LaboratoryStuff/Thorlabs/THR-100-010 Cage Slit 1mm/Photos/THR-100-010_Photo_02.JPG

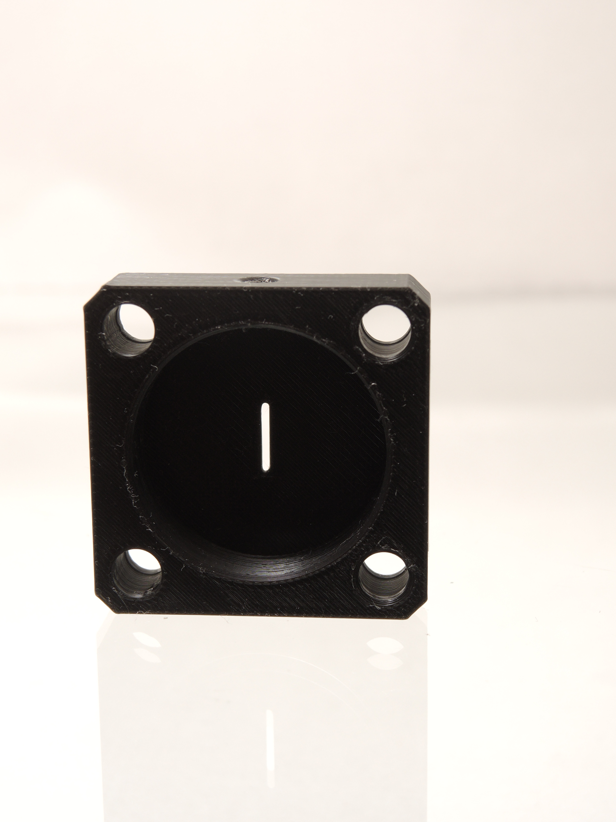
THR-100-010 Cage Slit 1mm/Photos/THR-100-010_Photo_02.JPG
