LaboratoryStuff/Thorlabs/THR-101-010 Cage Hamamatsu 14 x 14 mm/Drawing/THR-101-010-110_Drawing04.jpg

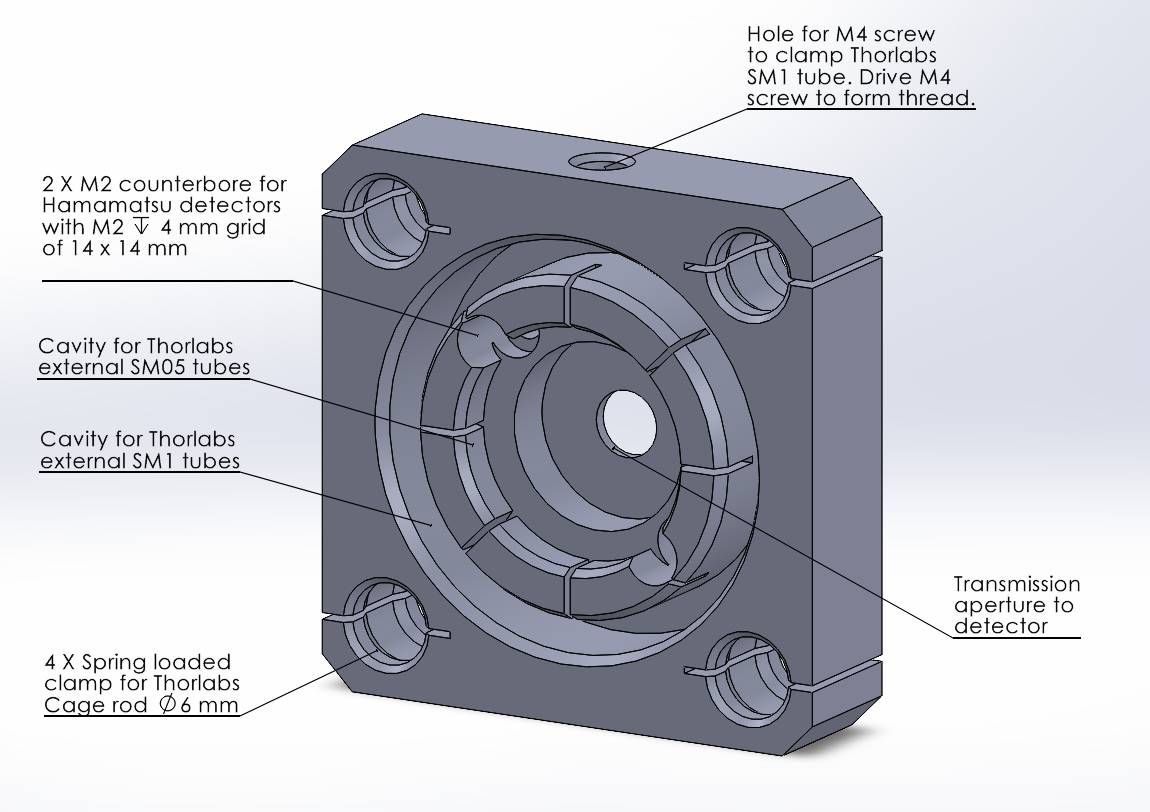
THR-101-010 Cage Hamamatsu 14 x 14 mm/Drawing/THR-101-010-110_Drawing04.jpg
