LaboratoryStuff/Thorlabs/THR-101-110 Cage Hamamatsu A3179/Photos/THR-101-110_Photo03.JPG

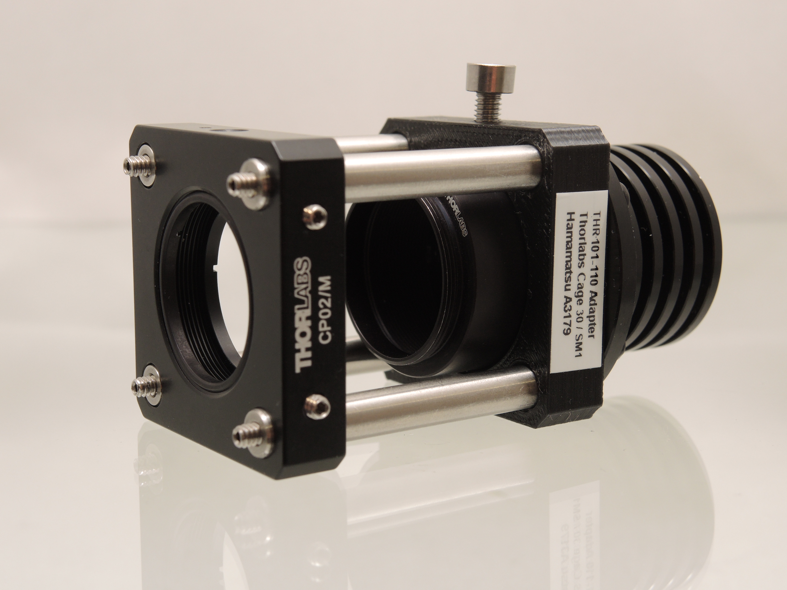
THR-101-110 Cage Hamamatsu A3179/Photos/THR-101-110_Photo03.JPG
