LaboratoryStuff/Thorlabs/THR-102-050 Aperture 5mm/Drawings/THR-102-050-110_Drawing04.jpg

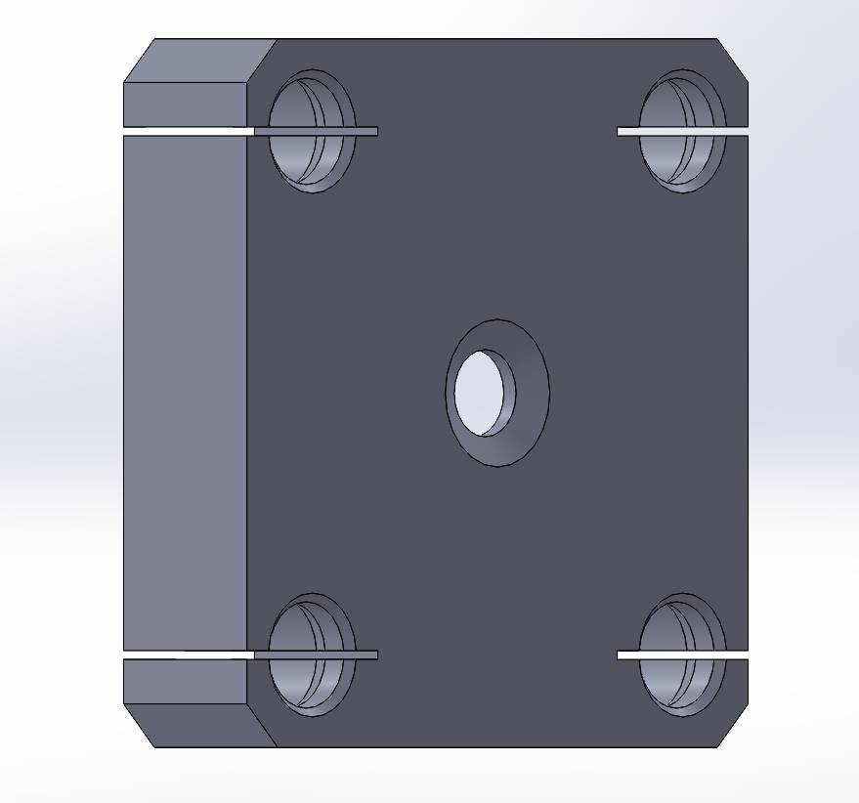
THR-102-050 Aperture 5mm/Drawings/THR-102-050-110_Drawing04.jpg
