LaboratoryStuff/Thorlabs/THR-102-050 Aperture 5mm/Photos/THR-102-050_Photo04.JPG

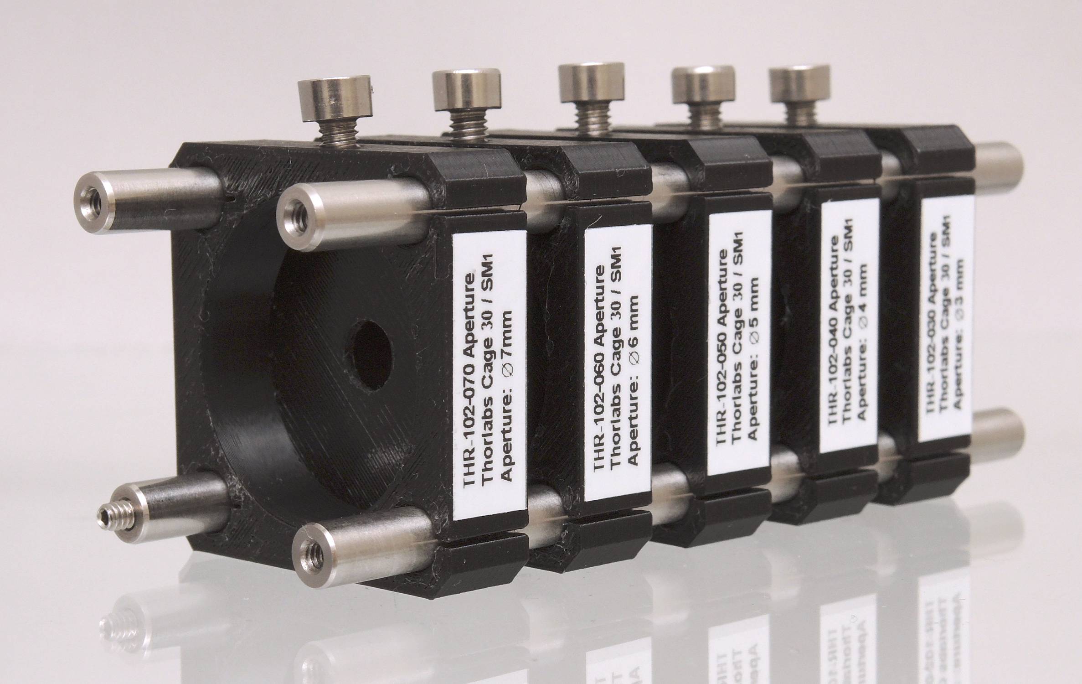
THR-102-050 Aperture 5mm/Photos/THR-102-050_Photo04.JPG
