LaboratoryStuff/Thorlabs/THR-120-010 Cage 60 SM2/Drawings/THR-120-010-010_Drawing03_cross-section.jpg

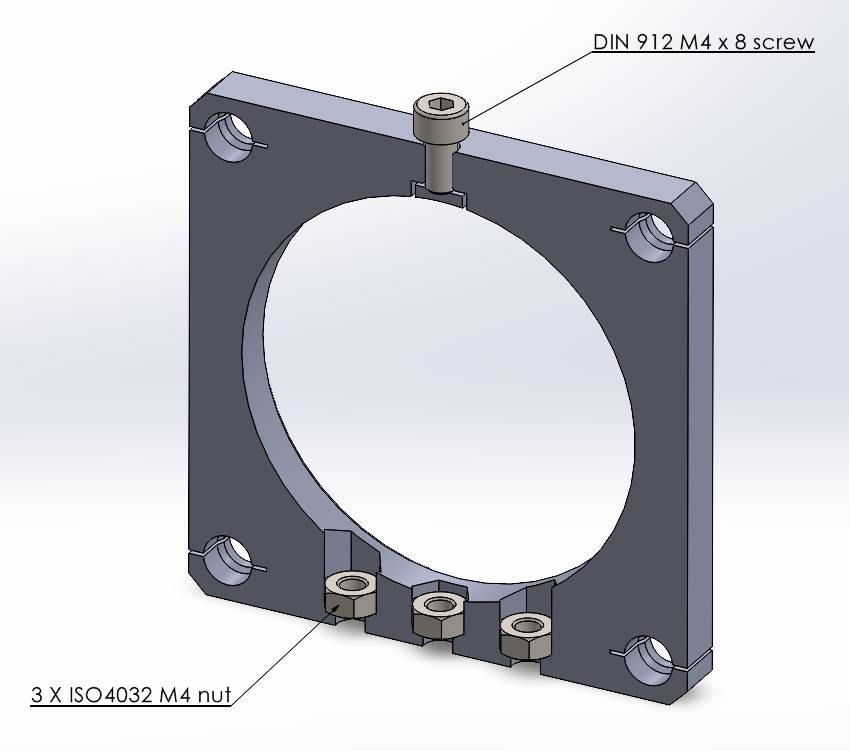
THR-120-010 Cage 60 SM2/Drawings/THR-120-010-010_Drawing03_cross-section.jpg
