LaboratoryStuff/Thorlabs/THR-120-010 Cage 60 SM2/Drawings/THR-120-010-110_Drawing02.jpg

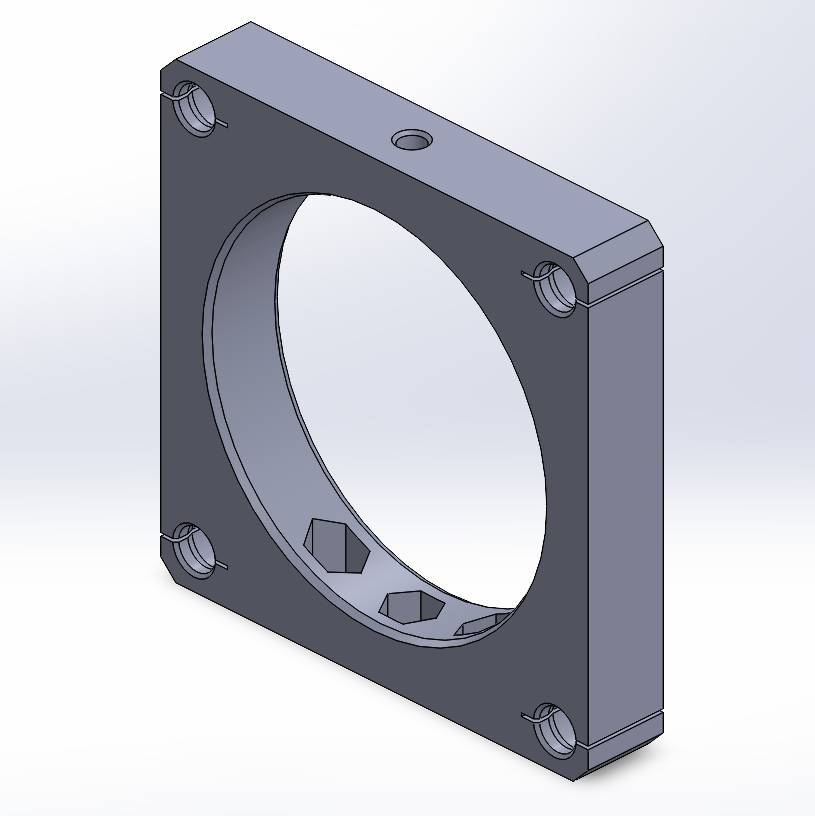
THR-120-010 Cage 60 SM2/Drawings/THR-120-010-110_Drawing02.jpg
