LaboratoryStuff/Thorlabs/THR-120-010 Cage 60 SM2/Drawings/THR-120-010-110_Drawing04_cross-section.jpg

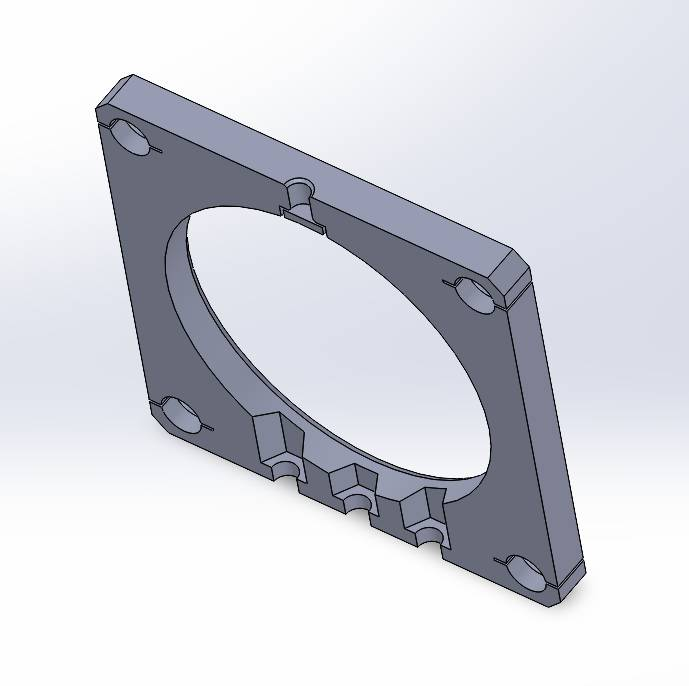
THR-120-010 Cage 60 SM2/Drawings/THR-120-010-110_Drawing04_cross-section.jpg
