LaboratoryStuff/Thorlabs/THR-120-010 Cage 60 SM2/Photos/THR-120-010_Photo_02_Add_Nut.JPG

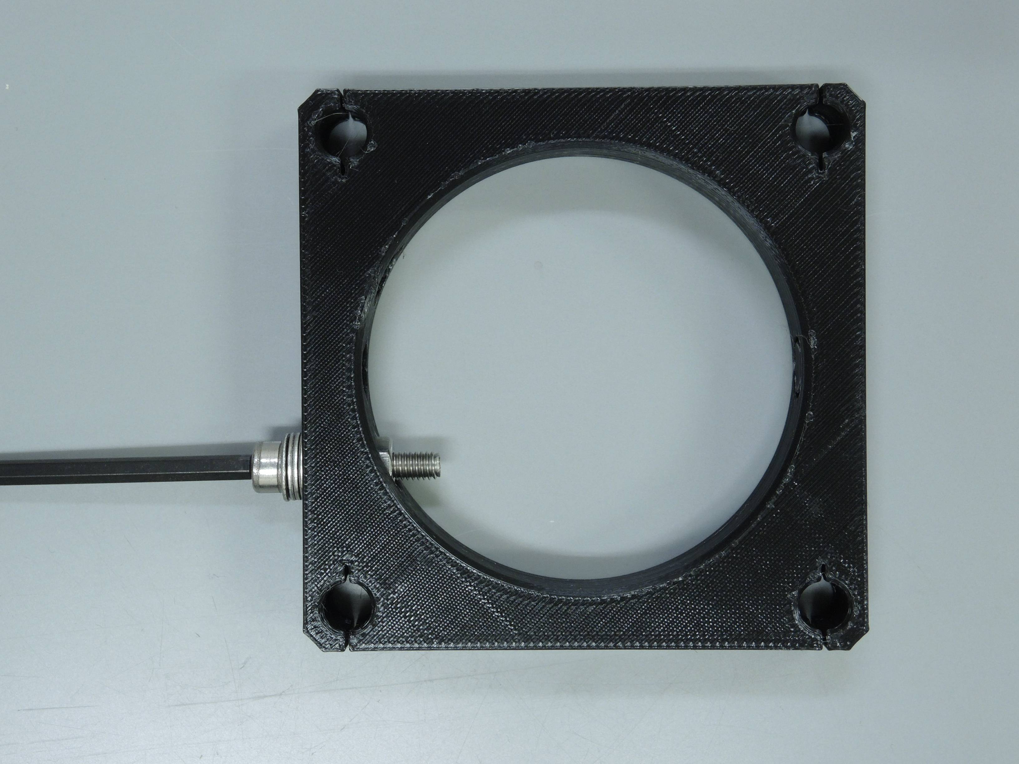
THR-120-010 Cage 60 SM2/Photos/THR-120-010_Photo_02_Add_Nut.JPG
