LaboratoryStuff/Thorlabs/THR-120-020 Cage 60 to 30/Drawings/THR-120-020-010_Drawing01_cross-section.jpg

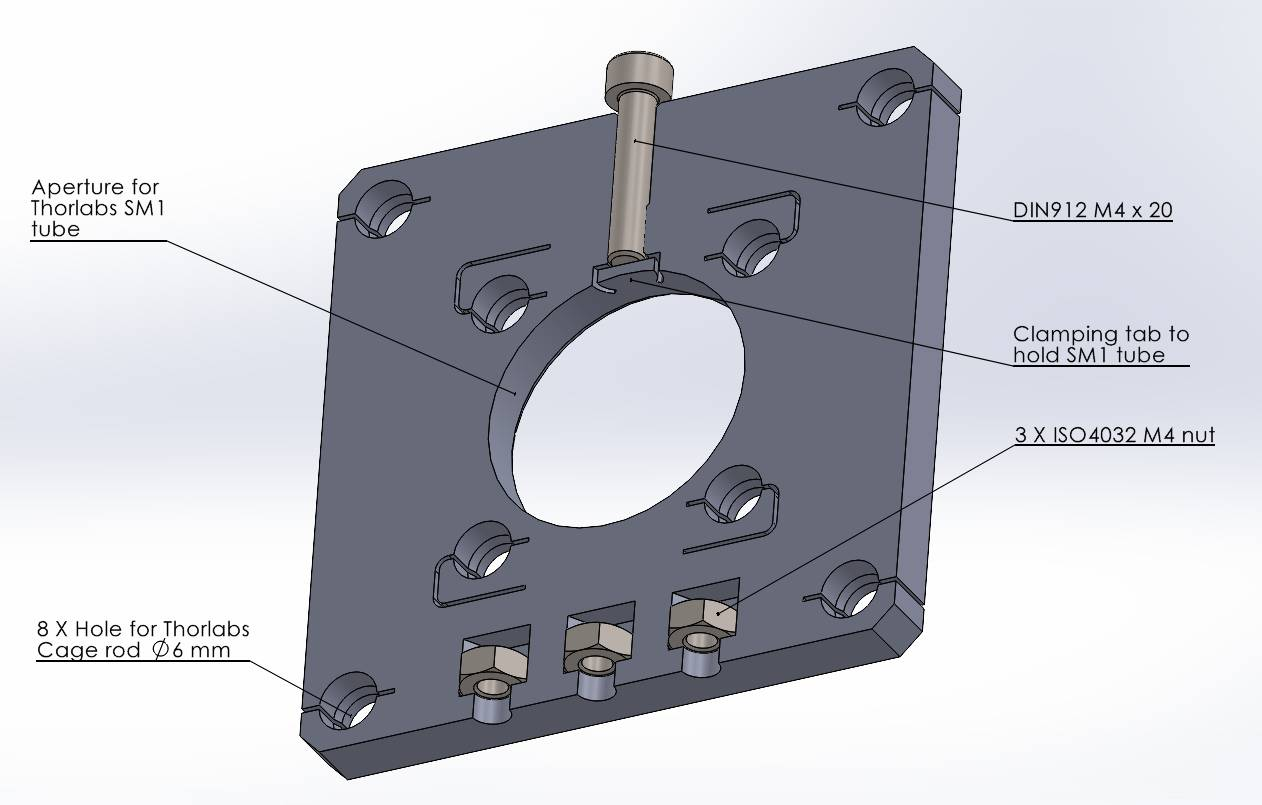
THR-120-020 Cage 60 to 30/Drawings/THR-120-020-010_Drawing01_cross-section.jpg
