LaboratoryStuff/Thorlabs/THR-120-020 Cage 60 to 30/Drawings/THR-120-020-110_Drawing03.jpg

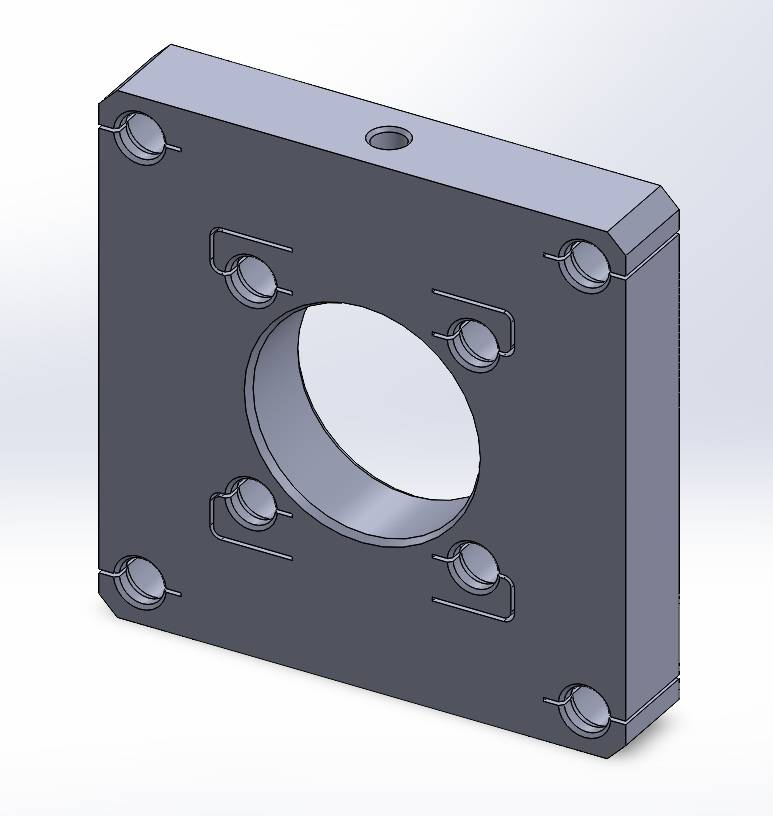
THR-120-020 Cage 60 to 30/Drawings/THR-120-020-110_Drawing03.jpg
