LaboratoryStuff/Thorlabs/THR-120-020 Cage 60 to 30/Photos/THR-120-020_Photo10.JPG

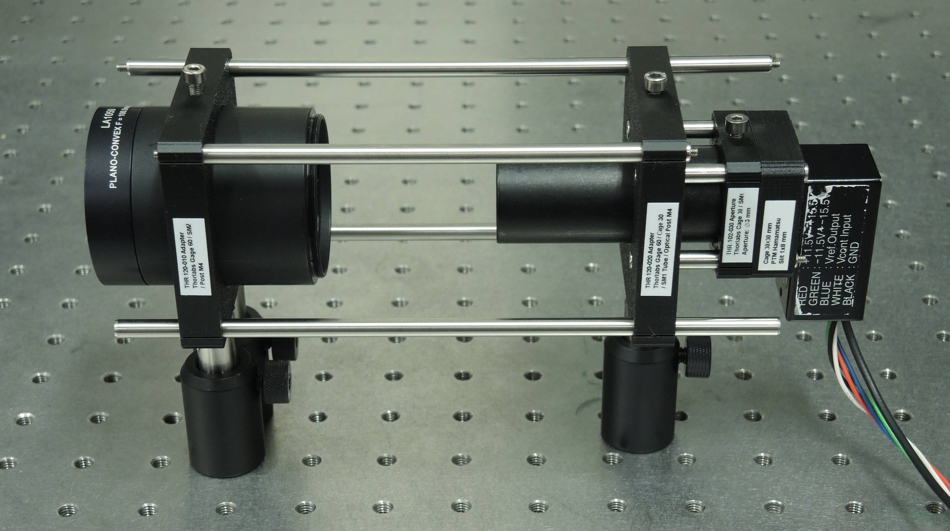
THR-120-020 Cage 60 to 30/Photos/THR-120-020_Photo10.JPG
